dgrover/flyception/myRIO/Camera/documentation/custom_fpga_block_diagram.gif

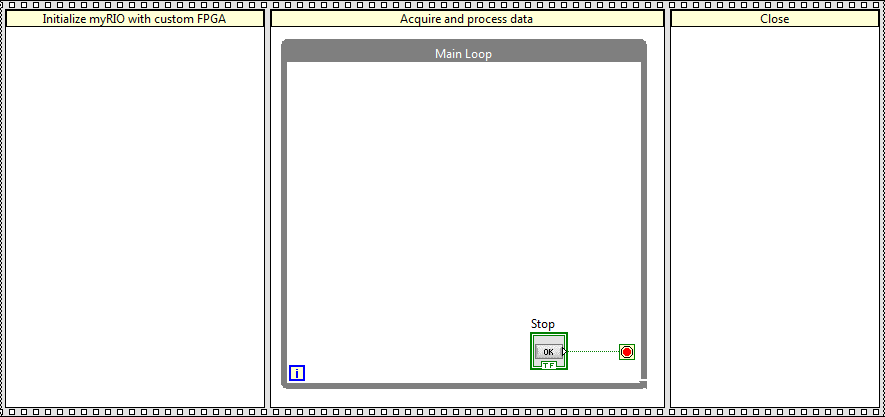
myRIO/Camera/documentation/custom_fpga_block_diagram.gif
