dgrover/flyception/calibration/arena/images_06192015/1.jpg

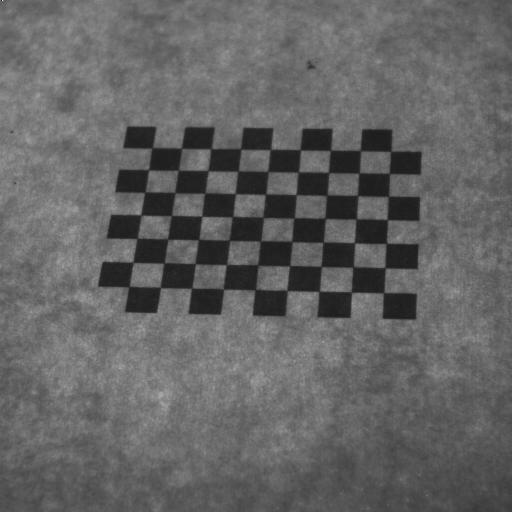
calibration/arena/images_06192015/1.jpg
