dgrover/flyception/calibration/arena/images_06192015/2.jpg

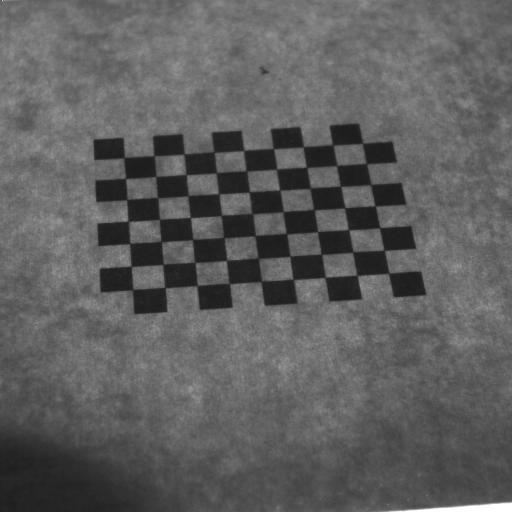
calibration/arena/images_06192015/2.jpg
