dgrover/flyception/calibration/arena/images_06192015/3.jpg

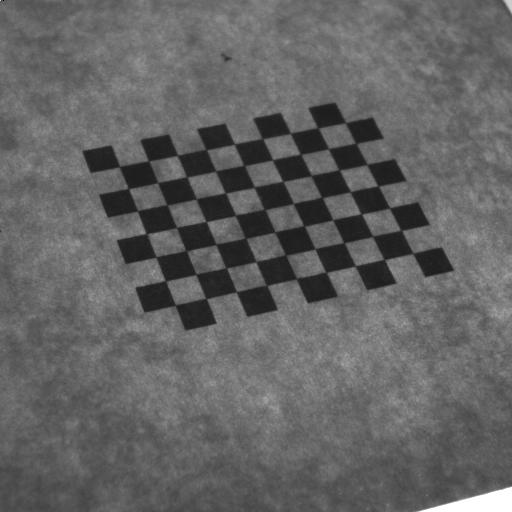
calibration/arena/images_06192015/3.jpg
