dgrover/flyception/calibration/arena/images_06192015/4.jpg

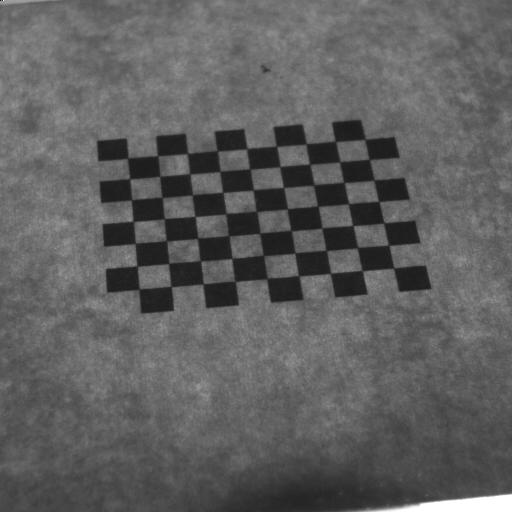
calibration/arena/images_06192015/4.jpg
