dgrover/flyception/calibration/arena/images_06192015/5.jpg

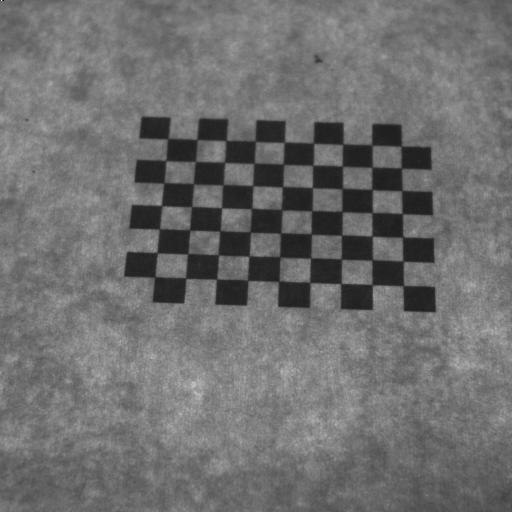
calibration/arena/images_06192015/5.jpg
