dgrover/flyception/calibration/arena/images_06192015/6.jpg

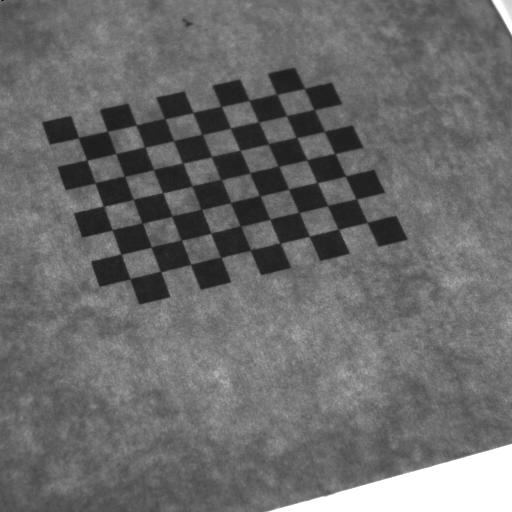
calibration/arena/images_06192015/6.jpg
