dgrover/flyception/calibration/arena/images_06192015/7.jpg

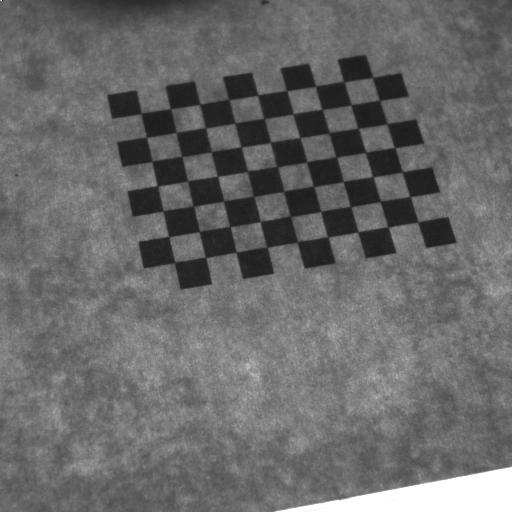
calibration/arena/images_06192015/7.jpg
