dgrover/flyception/calibration/arena/images_06192015/8.jpg

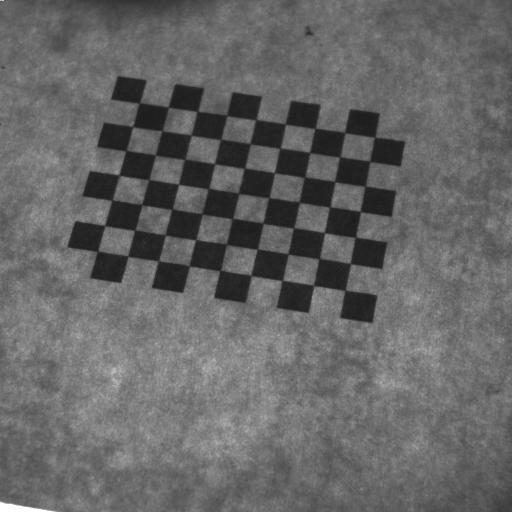
calibration/arena/images_06192015/8.jpg
