dgrover/flyception/calibration/arena/images_09192016/1.jpg

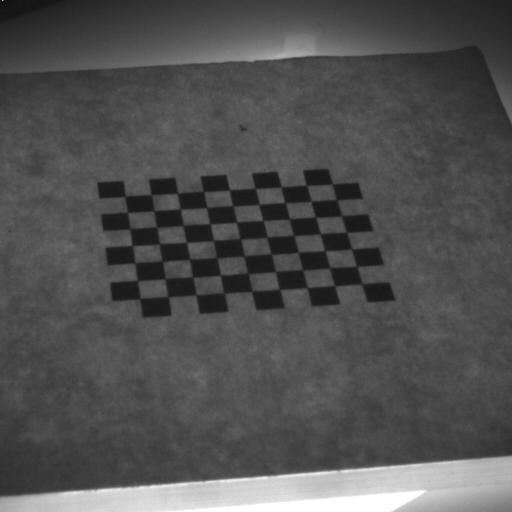
calibration/arena/images_09192016/1.jpg
