dgrover/flyception/calibration/arena/images_09192016/2.jpg

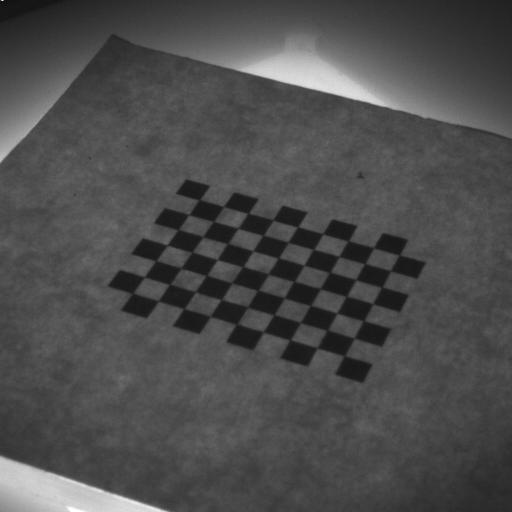
calibration/arena/images_09192016/2.jpg
