dgrover/flyception/calibration/arena/images_09192016/3.jpg

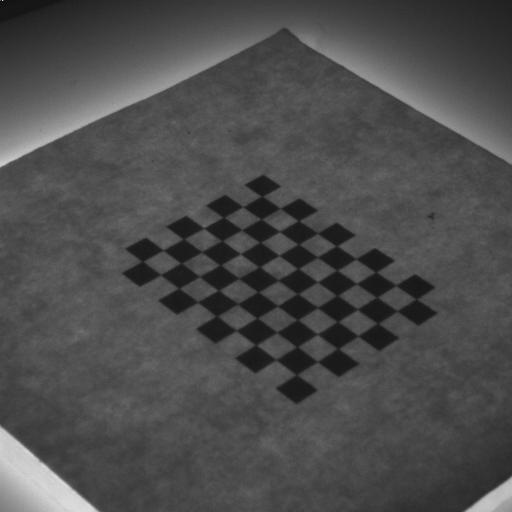
calibration/arena/images_09192016/3.jpg
