dgrover/flyception/calibration/arena/images_09192016/4.jpg

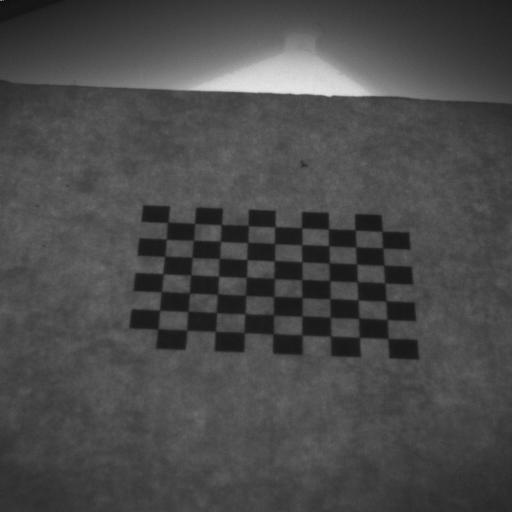
calibration/arena/images_09192016/4.jpg
