dgrover/flyception/calibration/arena/images_09192016/5.jpg

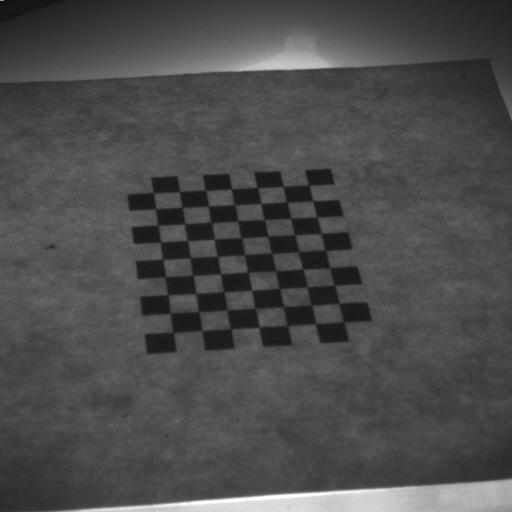
calibration/arena/images_09192016/5.jpg
