dgrover/flyception/calibration/arena/images_09192016/6.jpg

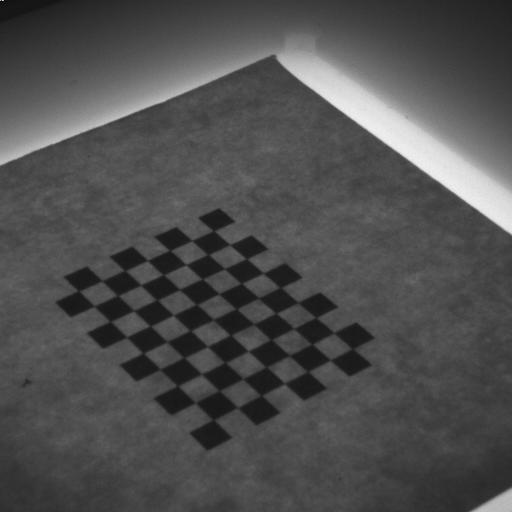
calibration/arena/images_09192016/6.jpg
