dgrover/flyception/calibration/arena/images_09192016/7.jpg

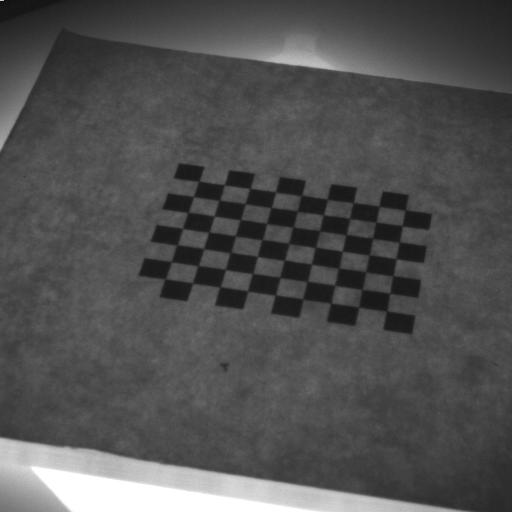
calibration/arena/images_09192016/7.jpg
