dgrover/flyception/calibration/arena/images_09192016/8.jpg

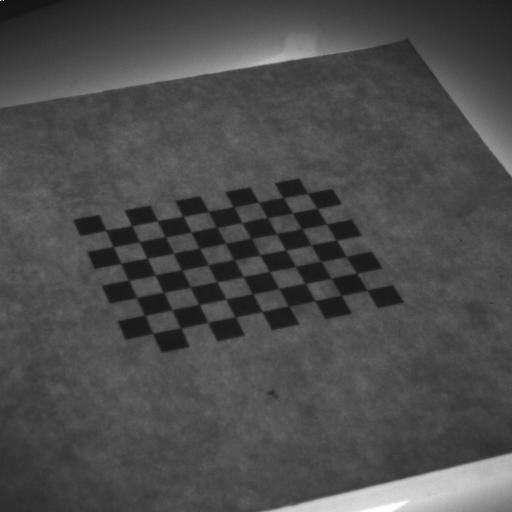
calibration/arena/images_09192016/8.jpg
