dgrover/flyception/calibration/arena/images_09192016/9.jpg

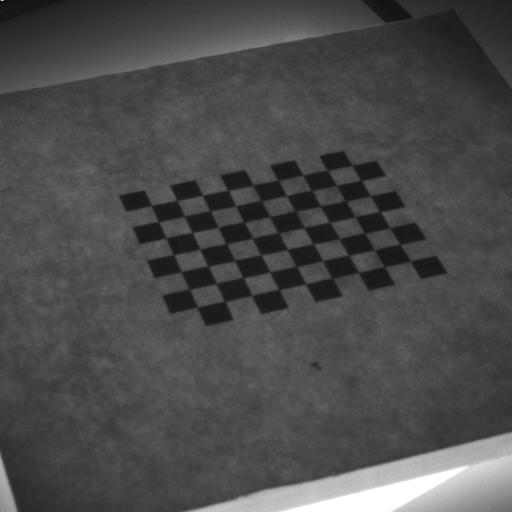
calibration/arena/images_09192016/9.jpg
