dgrover/flyception/calibration/arena/images_09192016/10.jpg

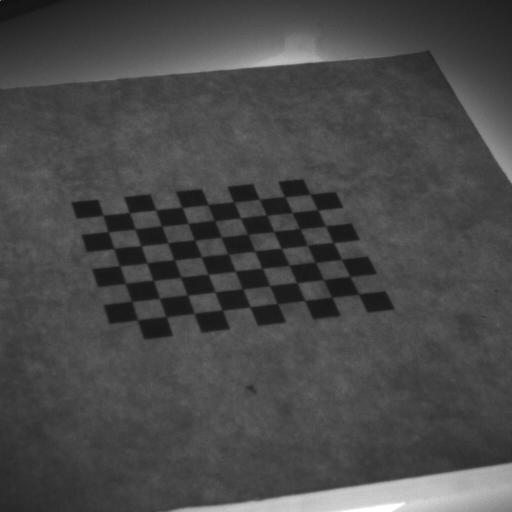
calibration/arena/images_09192016/10.jpg
