dgrover/flyception/calibration/arena/images_09192016/11.jpg

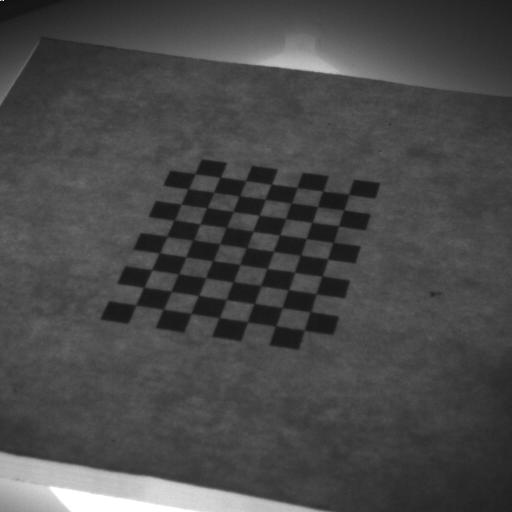
calibration/arena/images_09192016/11.jpg
