dgrover/flyception/calibration/arena/images_09192016/12.jpg

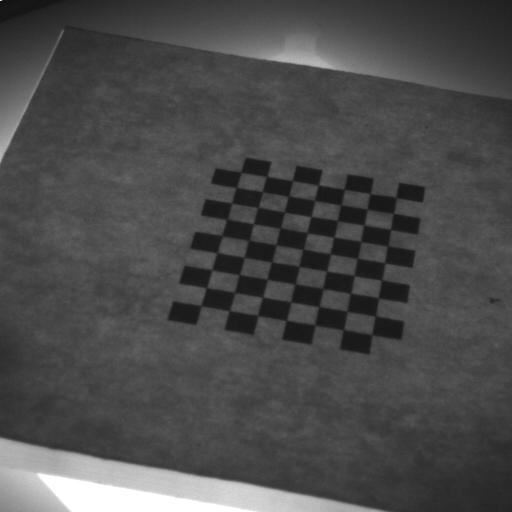
calibration/arena/images_09192016/12.jpg
