dgrover/flyception/calibration/arena/images_09192016/13.jpg

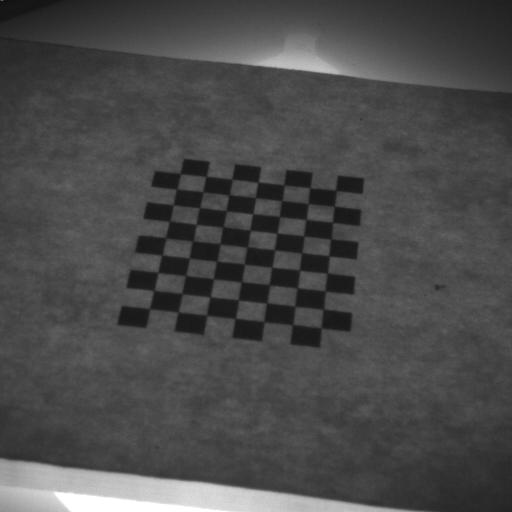
calibration/arena/images_09192016/13.jpg
